OLIMEX/RP2040-PICO-PC/HARDWARE/RP2040-PICO-PC hardware revision D/3d/SOD123.step

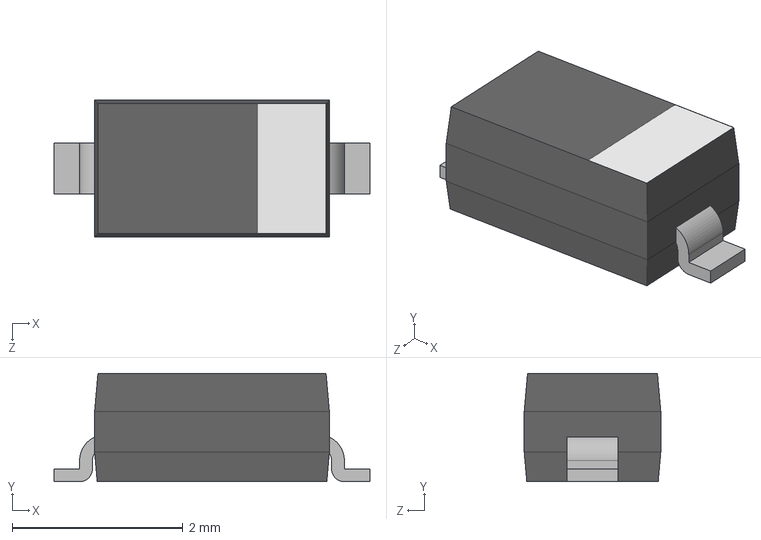
[picture p16: CAD file, 2025-03-31]
HARDWARE/RP2040-PICO-PC hardware revision D/3d/SOD123.step
3.70 x 1.27 x 1.60 mm
